ncicek/IQmodulator/rtl/fm_generator_wb_slave.v

`default_nettype none
`timescale 1 ns/100 ps  // time-unit = 1 ns, precision = 10 ps

module fm_generator_wb_slave (
    i_clk, i_reset, 
    i_wb_cyc, i_wb_stb, i_wb_we, i_wb_addr, i_wb_data, o_wb_ack, o_wb_stall, o_wb_data,
    o_dac_a_registered, o_dac_b_registered, o_cw_b
);
parameter sine_lookup_width = 16,
		phase_width = 12,
		accumulator_width = 32,
		output_dac_width = 10;
			
input wire i_clk, i_reset;
input wire i_wb_cyc, i_wb_stb, i_wb_we;
input wire [2:0] i_wb_addr;
input wire [31:0] i_wb_data;
output reg o_wb_ack;
output wire o_wb_stall;
output reg [31:0] o_wb_data;
output wire o_cw_b;
output reg [(output_dac_width-1):0] o_dac_a_registered, o_dac_b_registered;

wire [(output_dac_width-1):0] o_dac_a, o_dac_b;
always @(posedge i_clk) begin //register the outputs to meet timing
	o_dac_a_registered <= o_dac_a;
	o_dac_b_registered <= o_dac_b;
end

wire signed [(sine_lookup_width-1):0] o_sample_i, o_sample_q;

reg cw, cw_mux_dac_a_mux_sel;
wire [9:0] control_mode_dac_a;

wire [sine_lookup_width:0] o_sample_dc_offset_i, o_sample_dc_offset_q;

assign o_sample_dc_offset_i = o_sample_i_attenuated + 2**(sine_lookup_width);
assign o_sample_dc_offset_q = o_sample_q_attenuated + 2**(sine_lookup_width);
assign o_dac_a = cw_mux_dac_a_mux_sel ? control_mode_dac_a : o_sample_dc_offset_i[sine_lookup_width:(sine_lookup_width-output_dac_width+1)];
assign o_dac_b = o_sample_dc_offset_q[sine_lookup_width:(sine_lookup_width-output_dac_width+1)];

//Wishbone slave interface
parameter REG_CARRIER_CENTER_FREQUENCY = 0;
parameter REG_MODULATION_FREQUENCY = 1;
parameter REG_MODULATION_DEVIATION = 2;
parameter REG_I_SCALE = 3;
parameter REG_Q_SCALE = 4;
reg [31:0] addr_space [0:4];

always @(posedge i_clk or posedge i_reset) begin
	if (i_reset) begin
		addr_space[REG_CARRIER_CENTER_FREQUENCY] <= 32'd100000;
		addr_space[REG_MODULATION_FREQUENCY] <= 32'd96523;
		addr_space[REG_MODULATION_DEVIATION] <= 32'd0; //1250
		addr_space[REG_I_SCALE] <= 32'd8000;
		addr_space[REG_Q_SCALE] <= 32'd8000;
	end else begin
		if ((i_wb_stb)&&(i_wb_we)&&(!o_wb_stall)) begin
			addr_space[i_wb_addr] <= i_wb_data;
		end
	end
end

always @(posedge i_clk) begin
	o_wb_data <= addr_space[i_wb_addr];
end

always @(posedge i_clk) begin
	if (i_reset)
		o_wb_ack <= 1'b0;
	else
		o_wb_ack <= ((i_wb_stb)&&(!o_wb_stall));
end

assign o_wb_stall = 1'b0; //we can accept wb request on every clock cycle, no need to stall

reg [(accumulator_width-2):0] carrier_increment;

wire signed [(accumulator_width-2):0] carrier_center_increment;
wire signed [(accumulator_width-2):0] modulation_increment;
wire [13:0] modulation_deviation_amount;
assign carrier_center_increment = addr_space[REG_CARRIER_CENTER_FREQUENCY][(accumulator_width-2):0];
assign modulation_increment = addr_space[REG_MODULATION_FREQUENCY][(accumulator_width-2):0];
assign modulation_deviation_amount = addr_space[REG_MODULATION_DEVIATION][13:0];

wire signed [(sine_lookup_width-1):0] modulation_output;

dds #( 	.sine_lookup_width(sine_lookup_width),
		.phase_width(phase_width),
		.accumulator_width(accumulator_width)
	) carrier(.i_clk(i_clk), .i_reset(i_reset), .i_ce(1'b1), .i_update(1'b1), .i_increment(carrier_increment), .o_sample_i(o_sample_i), .o_sample_q(o_sample_q));

dds #( 	.sine_lookup_width(sine_lookup_width),
		.phase_width(phase_width),
		.accumulator_width(accumulator_width)
	) modulation(.i_clk(i_clk), .i_reset(i_reset), .i_ce(1'b1), .i_update(1'b1), .i_increment(modulation_increment), .o_sample_i(modulation_output), .o_sample_q());


wire [13:0] i_scale, q_scale;
assign i_scale = addr_space[REG_I_SCALE][13:0];
assign q_scale = addr_space[REG_Q_SCALE][13:0];
wire signed [(sine_lookup_width-1):0] o_sample_i_attenuated, o_sample_q_attenuated;
wire signed [29:0] o_sample_i_scaled, o_sample_q_scaled;
/* verilator lint_off WIDTH */
assign o_sample_i_attenuated = o_sample_i_scaled>>>14;
assign o_sample_q_attenuated = o_sample_q_scaled>>>14;
/* verilator lint_on WIDTH */
sgnmpy_14x16 i_gain_multiplier(i_clk, i_reset, 1'b1, i_scale, o_sample_i, 1'b0, o_sample_i_scaled);
sgnmpy_14x16 q_gain_multiplier(i_clk, i_reset, 1'b1, q_scale, o_sample_q, 1'b0, o_sample_q_scaled);


wire signed [29:0] carrier_center_increment_offset;
sgnmpy_14x16 modulation_amplitude_multiplier(i_clk, i_reset, 1'b1, modulation_deviation_amount, modulation_output, 1'b0, carrier_center_increment_offset);

always @(posedge i_clk or posedge i_reset) begin
	if (i_reset) begin
		carrier_increment <= {(31){1'b0}};
	end else begin
		carrier_increment <= carrier_center_increment + carrier_center_increment_offset;
	end
end

//Init control programming
assign o_cw_b = ~cw;
wire control_pd, control_dacen, control_ide, control_ren_b;
wire [3:0] control_g;

assign control_mode_dac_a[9] = control_pd;
assign control_mode_dac_a[8] = control_dacen;
assign control_mode_dac_a[7] = control_ide;
assign control_mode_dac_a[6] = control_ren_b;
assign control_mode_dac_a[5:2] = control_g;
assign control_mode_dac_a[1:0] = 2'bxx;

assign control_pd = 1'b0;
assign control_dacen = 1'b1;
assign control_ide = 1'b0;
assign control_ren_b = 1'b0;
assign control_g = 4'b1000;

reg [3:0] startup_timer;
always @(posedge i_clk or posedge i_reset) begin
	if (i_reset) begin
		startup_timer <= 4'b0;
	end else begin
		if (startup_timer == 4'd3) begin
			cw <= 1'b1;
			cw_mux_dac_a_mux_sel <= 1'b1;
		end else if (startup_timer == 4'd10) begin
			cw <= 1'b0;
		end else if (startup_timer == 4'd15) begin
			cw_mux_dac_a_mux_sel <= 1'b0;
		end
		if (startup_timer != 4'b1111) begin
			startup_timer <= startup_timer + 1'b1;
		end
	end
end


endmodule
`default_nettype wire
