ncicek/IQmodulator/rtl/bimpy.v

////////////////////////////////////////////////////////////////////////////////
//
// Filename: 	bimpy
//
// Project:	A multiply core generator
//
// Purpose:	An unsigned 2-bit multiply based upon the fact that LUT's allow
//		6-bits of input, but a 2x2 bit multiply will never carry more
//	than one bit.  While this multiply is hardware independent, it is
//	really motivated by trying to optimize for a specific piece of
//	hardware (Xilinx-7 series ...) that has 4-input LUT's with carry
//	chains.
//
// Creator:	Dan Gisselquist, Ph.D.
//		Gisselquist Technology, LLC
//
////////////////////////////////////////////////////////////////////////////////
//
// Copyright (C) 2015-2020, Gisselquist Technology, LLC
//
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
// This program is distributed in the hope that it will be useful, but WITHOUT
// ANY WARRANTY; without even the implied warranty of MERCHANTIBILITY or
// FITNESS FOR A PARTICULAR PURPOSE.  See the GNU General Public License
// for more details.
//
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
// License:	GPL, v3, as defined and found on www.gnu.org,
//		http://www.gnu.org/licenses/gpl.html
//
//
////////////////////////////////////////////////////////////////////////////////
module	bimpy(i_clk, i_reset, i_ce, i_a, i_b, o_r);
	parameter	BW=18; // Number of bits in i_b
	localparam	LUTB=2;// Number of bits in i_a for our LUT multiply
	input	wire			i_clk, i_reset, i_ce;
	input	wire	[(LUTB-1):0]	i_a;
	input	wire	[(BW-1):0]	i_b;
	output	reg	[(BW+LUTB-1):0]	o_r;

	wire	[(BW+LUTB-2):0]	w_r;
	wire	[(BW+LUTB-3):1]	c;

	assign	w_r =  { ((i_a[1])?i_b:{(BW){1'b0}}), 1'b0 }
				^ { 1'b0, ((i_a[0])?i_b:{(BW){1'b0}}) };
	assign	c = { ((i_a[1])?i_b[(BW-2):0]:{(BW-1){1'b0}}) }
			& ((i_a[0])?i_b[(BW-1):1]:{(BW-1){1'b0}});

	initial	o_r = 0;
	always @(posedge i_clk)
	if (i_reset)
		o_r <= 0;
	else if (i_ce)
		o_r <= w_r + { c, 2'b0 };

`ifdef	FORMAL
	reg	f_past_valid;

	initial	f_past_valid = 1'b0;
	always @(posedge i_clk)
	f_past_valid <= 1'b1;

`define	ASSERT	assert

	always @(posedge i_clk)
	if ((f_past_valid)&&($past(i_ce)))
	begin
		if ($past(i_a)==0)
			`ASSERT(o_r == 0);
		else if ($past(i_a) == 1)
			`ASSERT(o_r == $past(i_b));

		if ($past(i_b)==0)
			`ASSERT(o_r == 0);
		else if ($past(i_b) == 1)
			`ASSERT(o_r[(LUTB-1):0] == $past(i_a));
	end
`endif
endmodule
